jmamma/MegaCommand_Design/1_0_2/diagrams/expansion_port_pins.png

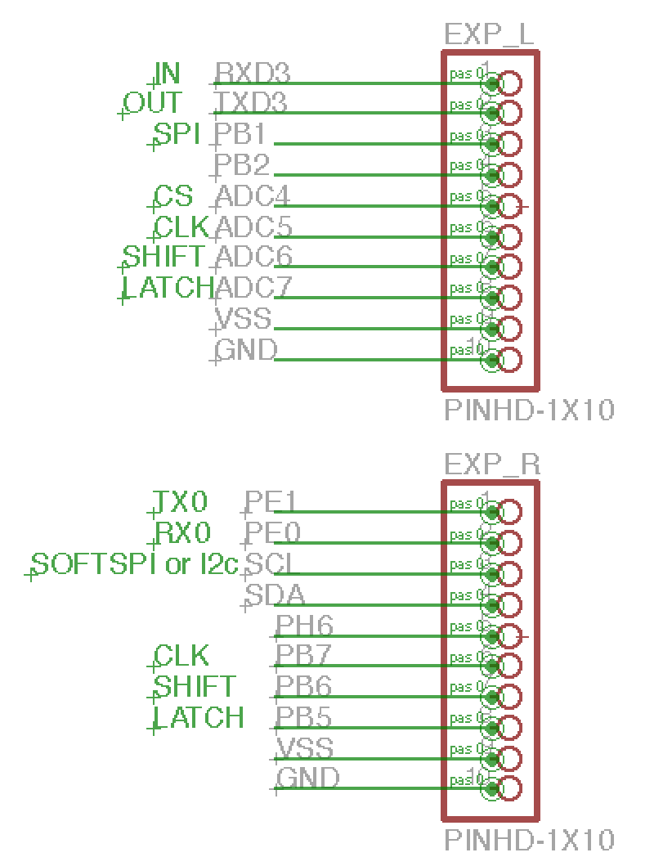
1_0_2/diagrams/expansion_port_pins.png
