jmamma/MegaCommand_Design/1_0_2/photos/IMG_0832.jpg

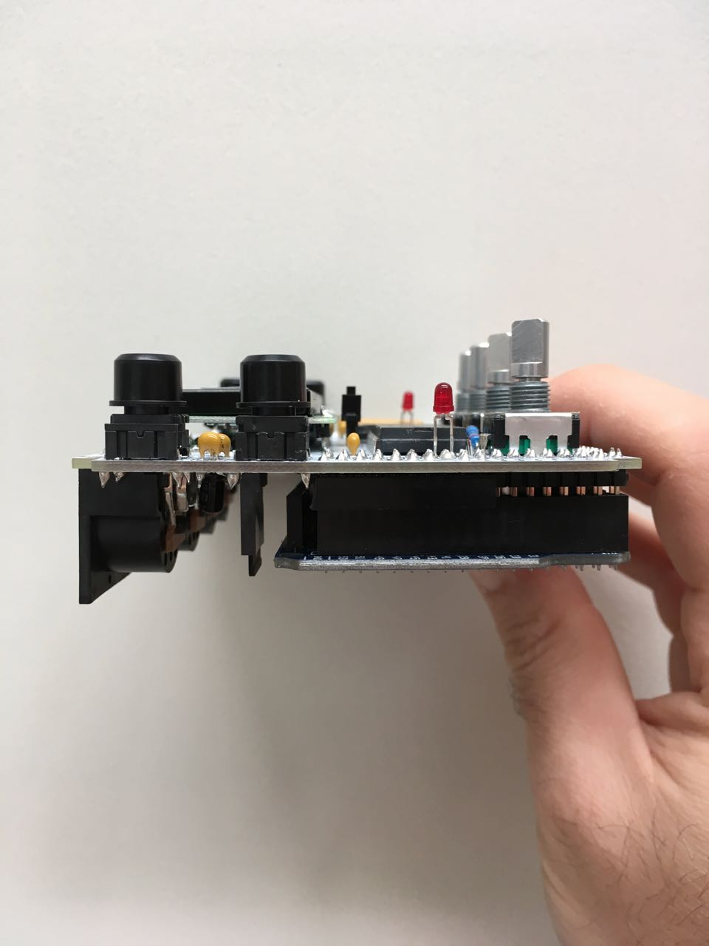
1_0_2/photos/IMG_0832.jpg
