jmamma/MegaCommand_Design/Enclosure/MegaCommand_DIY/Router Design/images/3D1.JPG

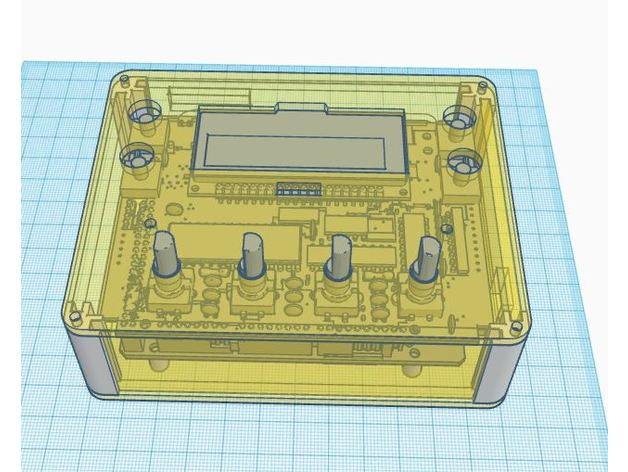
Enclosure/MegaCommand_DIY/Router Design/images/3D1.JPG
