jmamma/MegaCommand_Design/Enclosure/MegaCommand_DIY/Router Design/images/3D2.JPG

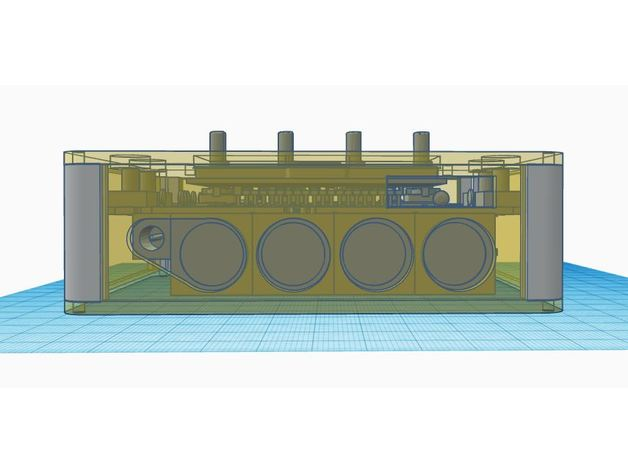
Enclosure/MegaCommand_DIY/Router Design/images/3D2.JPG
