jmamma/MegaCommand_Design/Enclosure/MegaCommand_DIY/Router Design/images/20221020_091426.jpg

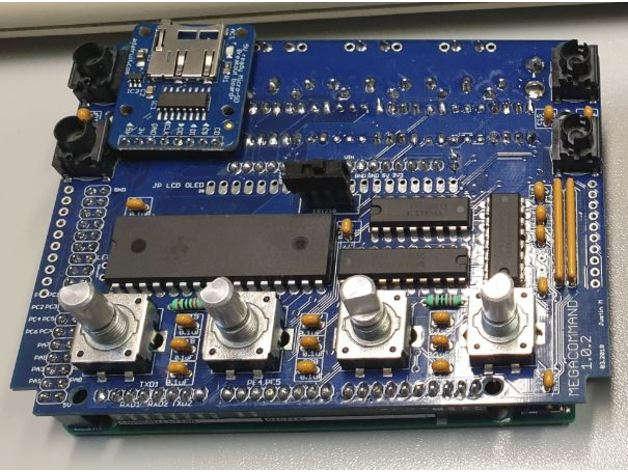
Enclosure/MegaCommand_DIY/Router Design/images/20221020_091426.jpg
