jmamma/MegaCommand_Design/Enclosure/MegaCommand_DIY/Router Design/images/20221028_100242.jpg

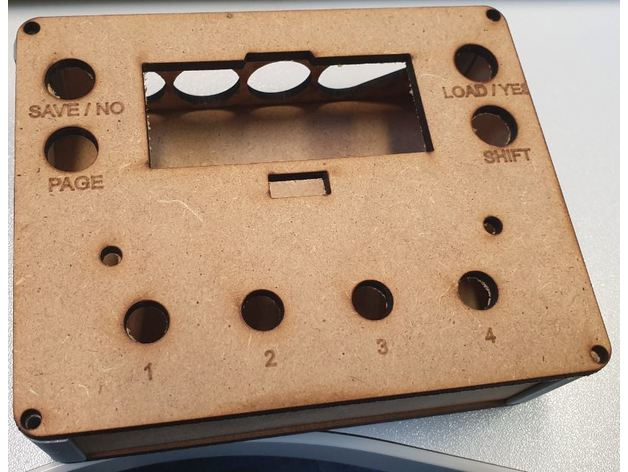
Enclosure/MegaCommand_DIY/Router Design/images/20221028_100242.jpg
