jmamma/MegaCommand_Design/Enclosure/MegaCommand_DIY/Router Design/images/20221028_100910.jpg

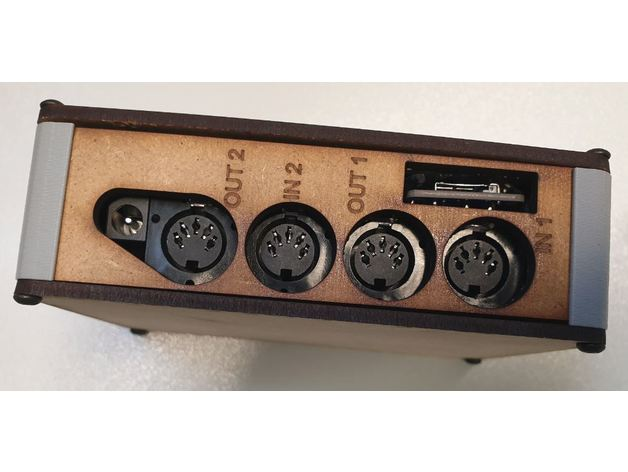
Enclosure/MegaCommand_DIY/Router Design/images/20221028_100910.jpg
