jmamma/MegaCommand_Design/Enclosure/MegaCommand_DIY/Router Design/images/BoxCorner.png

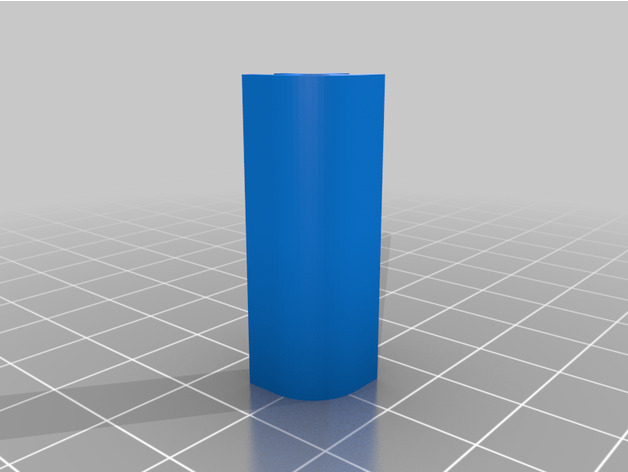
Enclosure/MegaCommand_DIY/Router Design/images/BoxCorner.png
