jmamma/MegaCommand_Design/pcb_fabrication_preferences.jpg

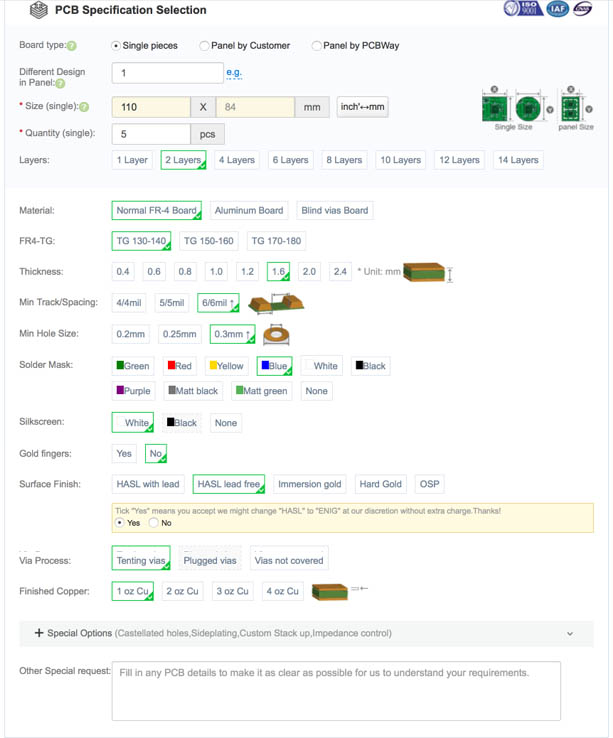
pcb_fabrication_preferences.jpg
